mohamedyanis/STM32L0-ESP32-Breakout-Board/Images/Block Diagram/STM32L0-ESP32-Block-Diagram.drawio.png

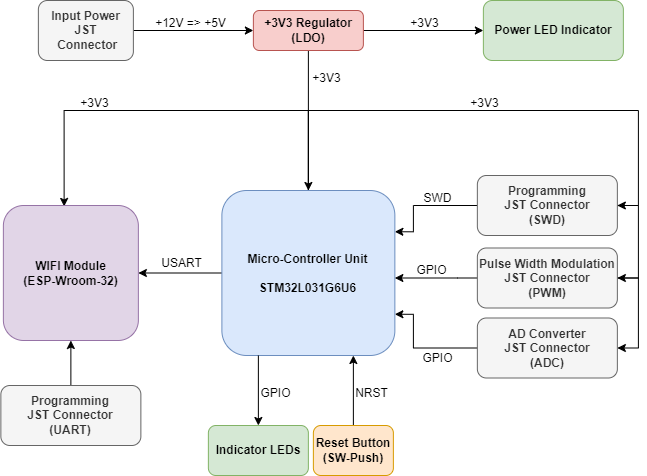
Images/Block Diagram/STM32L0-ESP32-Block-Diagram.drawio.png
